Borval99/BombonieraElettronica/LTspice/Draft1.asc

C1: cap; 100n
C2: cap; 100n
C3: cap; 1n
C4: cap; 1n
C5: cap; 100n
C6: cap; 100n
C7: cap; 100n
D1: diode; 1N4148
D2: LED; LY_L29K_typ
D3: LED; LY_L29K_typ
D4: diode; 1N4148
D5: LED; LY_L29K_typ
D6: LED; LY_L29K_typ
M1: pmos; DMG1013T
Q1: npn; BC817-40
Q2: npn; BC817-40
Q3: npn; BC817-40
Q5: npn; BC817-40
Q6: pnp; BC807_25L
Q7: pnp; BC807_25L
R1: res; 100k
R2: res; 100k
R3: res; 100k
R4: res; 1Meg
R5: res; 1Meg
R6: res; 200
R7: res; 200
R8: res; 100k
R9: res; 1Meg
R10: res; 1Meg
R11: res; 100k
R12: res; 100k
R13: res; 100k
R14: res; 100k
R15: res; 1Meg
R16: res; 1Meg
R17: res; 1Meg
R18: res; 500
R20: res; 500
S1: sw; MYSW
U1: T2N7002AK_G0_00
U2: T2N7002AK_G0_00
U3: T2N7002AK_G0_00
U4: T2N7002AK_G0_00
V1: voltage; PULSE(0 5 0 10u 10u 0.1 5 5)
V2: voltage; 2.5
V3: voltage; 3
Named nets: 0
.tran 5 startup
.MODEL LY_L29K_typ D
+ IS=1.312707786933147e-22
+ N=1.578286320648063
+ RS=3.705549613591443
+ Tnom=25
+ mfg=OSRAM_OS
.SUBCKT BSS84AKM DRAIN GATE SOURCE
 
LD DRAIN 5 4e-10
RLD2 DRAIN 5 1.0053088
RLD1 5 4 0.0023
LG GATE 1 8.81711084834576e-10
RLG GATE 1 2.21597978160436
LS SOURCE 8 1.37135823401249e-09
RLS2 SOURCE 8 3.44659625151304
RLS1 8 7 0.0585579563006914
 
RDS 7 4 50000000000 TC=-0.05
 
RS 6 7 0.0001
 
RD 3 4 3.40064204369931 TC=0.0107436954098734,-5.13207197144137e-06
RBD 9 4 0.114762406260949 TC=0.0107436954098734,-5.13207197144137e-06
DBD 9 7 DBD
 
M1 3 2 6 6 MINT
 
RGS 2 6 38095238.0952381
CGS 2 6 2.37e-11
RG 1 2 19.9470486389713
 
* CGD
C11    11   12   1E-12
V11    11   0   0Vdc
G11    2 3 VALUE { V(13, 0)*I(V11) }
E11    12   0  2 3  1
E12    13   0  TABLE {V(12)}
+ -20           19.46
+ -15           19.50
+ -10           19.85
+ -5            20.39
+ -4            20.35
+ -3            19.61
+ -2            14.64
+ -1            7.77
+ -0.5          5.76
+ -0.2          4.69
+ -0.1          4.37
+ 0             4.08
+ 0.1           3.78
+ 0.2           3.51
+ 0.5           2.89
+ 1             2.42
+ 2             2.1
+ 3             1.94
+ 4             1.84
+ 5             1.76
+ 6             1.71
+ 8             1.62
+ 10            1.55
+ 12            1.5
+ 15            1.43
+ 20            1.35
+ 30            1.25
+ 40            1.19
 

 
.MODEL MINT PMOS(Vto=-1.66 Kp=1.3807e-01 Nfs=1000000000 Eta=0
+ Level=3 L=1e-4 W=1e-4 Gamma=0 Phi=0.6 Is=1e-24
+ Js=0 Pb=0.8  Cj=0 Cjsw=0 Cgso=0 Cgdo=0 Cgbo=0
+ Tox=1e-07 Xj=0  
+ U0=600 Vmax=3000)
*+ U0=600 Vmax=1000)
 
.MODEL DBD D(Bv=63.00 Ibv=2.00E-06 Rs=1E-6 Is=1.48118796889277e-15
+ N=1 M=0.33 VJ=0.53 Fc=0.5 Cjo=1.144e-11 Tt=1.85e-08)
 
.ENDS
.model MYSW SW(Ron = .01 Roff= 10G Vt = 2.5 Vh = -.5)
.SUBCKT DMG1013T   10 20 30
*     TERMINALS:  D  G  S
M1   1  2  3  3  PMOS L=0.6U W=47.66m
RD  10  1  300m
RS  30  3  85m
RG  20  2  1
CGS  2  3  57.55p
EGD 12  30  2  1  1
VFB 14  30  0
FFB  2  1  VFB  1
CGD 13 14  22.2p
R1  13  30  1.00
D1  13 12  DLIM
DDG 14 15  DCGD
R2  12 15  1.00
D2  30  15  DLIM
DSD 10  3  DSUB
.MODEL PMOS PMOS LEVEL=3 U0=200 VMAX=40k
+ ETA=0.1m VTO=-0.952 TOX=20n NSUB=2.1e16
.MODEL DCGD D CJO=22.2p VJ=0.150 M=0.320
.MODEL DSUB D IS=36.1n N=1.50 RS=21.8m BV=20.0
+ CJO=20p VJ=0.600 M=0.50
.MODEL DLIM D IS=100U
.ENDS
**********************************************************
*
* BC807_25L
*
* Nexperia
*
* General purpose PNP transistor
* IC   = 500 mA
* VCEO = 45 V 
* hFE  = 160 - 400 @ 1V/100mA
* 
*
*
*
* Package pinning does not match Spice model pinning.
* Package: SOT 23
* 
* Package Pin 1: Base
* Package Pin 2: Emitter
* Package Pin 3: Collector
*
*
* Extraction date (week/year): 48/2017 
* Spicemodel includes temperature dependency
*
**********************************************************
*#
.SUBCKT BC807_25L 1 2 3
*
* Diode D1, transistor Q2 and resistor RQ 
* are dedicated to improve modeling of quasi
* saturation area and reverse mode operation
* and do not reflect physical devices.
*
Q1 1 2 3 MAIN 0.9306 
Q2 11 2 3 MAIN 0.06942
RQ 11 1 50.53 
D1 1 2 DIODE
*
.MODEL MAIN PNP 
+ IS = 5.878E-014
+ NF = 0.9745
+ ISE = 2.667E-014
+ NE = 1.492
+ BF = 280
+ IKF = 0.4297
+ VAF = 29.81
+ NR = 0.9743
+ ISC = 2.294E-014
+ NC = 1.174
+ BR = 27.66
+ IKR = 0.5785
+ VAR = 25
+ RB = 200
+ IRB = 2E-005
+ RBM = 1
+ RE = 0.3749
+ RC = 0.1213
+ XTB = 1.866
+ EG = 1.11
+ XTI = 10.99
+ CJE = 5.138E-011
+ VJE = 0.655
+ MJE = 0.345
+ TF = 1.05E-009
+ XTF = 1.859
+ VTF = 3.813
+ ITF = 0.4393
+ PTF = 0
+ CJC = 1.686E-011
+ VJC = 0.5341
+ MJC = 0.36
+ XCJC = 0.459
+ TR = 6.1E-008
+ CJS = 0
+ VJS = 0.75
+ MJS = 0.333
+ FC = 0.85
.MODEL DIODE D
+ IS = 5.278E-016
+ N = 0.9309
+ BV = 1000
+ IBV = 0.001
+ RS = 2883
+ CJO = 0
+ VJ = 1
+ M = 0.5
+ FC = 0
+ TT = 0
+ EG = 1.11
+ XTI = 3
.ENDS
*
