Borval99/BombonieraElettronica/LTspice/Draft2.asc

R_Shunt: res; 0.09 Ohm
Scheda di alimentazione
Oscilloscopio
Alimentatore 
da banco
-
+
-
+
CH1
CH2
GND
